Aviancer/amouse/diagrams/amouse-kicad/amouse.sch

## KiCad design diagrams/amouse-kicad/amouse.sch (2021-07-27, an earlier design)

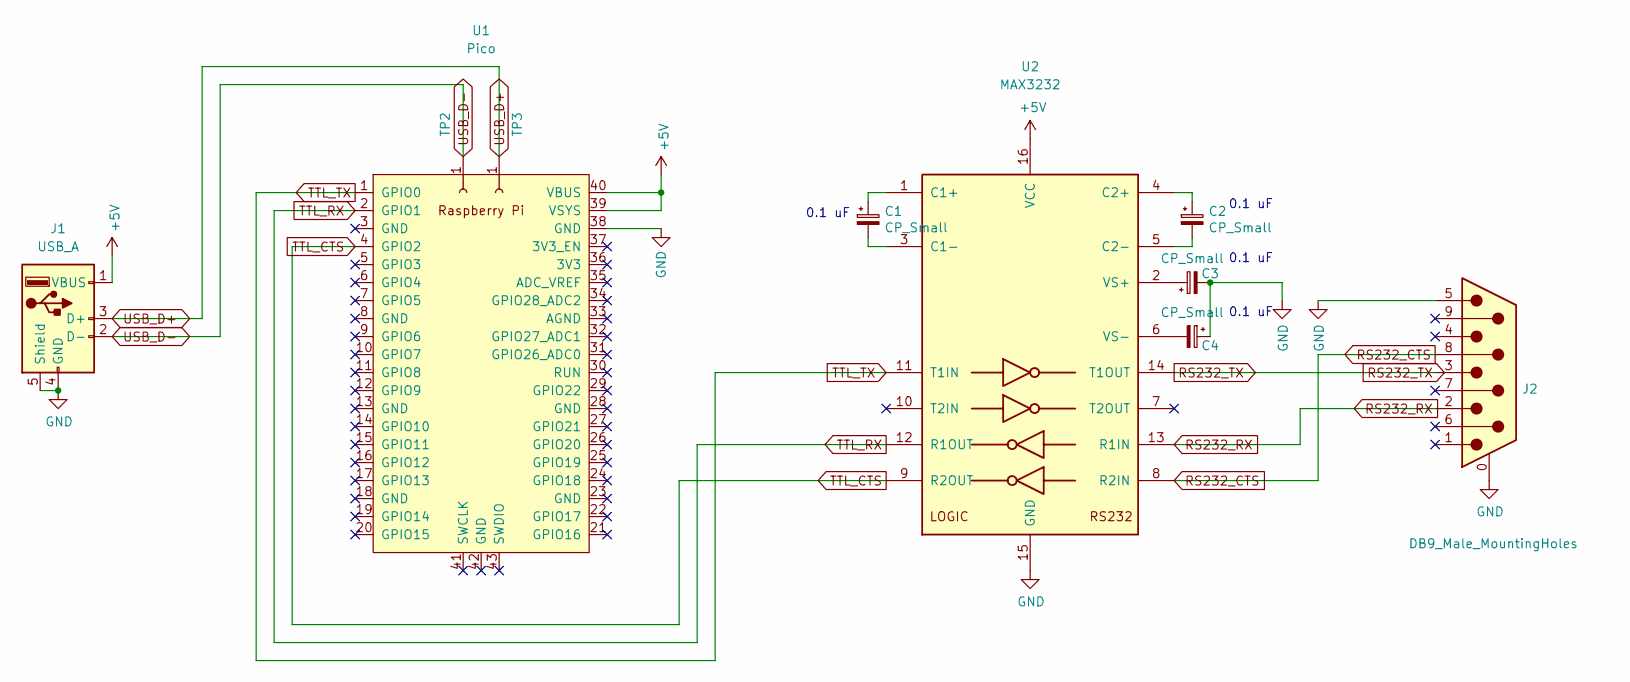
[picture p3: schematic amouse.sch]

Parts:
C1, C2, C3, C4: CP_Small
J1: USB_A
J2: DB9_Male_MountingHoles
TP2: TP2
TP3: TP3
U1: Pico; RPi_Pico_SMD_TH
U2: MAX3232

Connections:
+5V: J1.1 (VBUS), U1.39 (VSYS), U1.40 (VBUS), U2.16 (VCC)
GND: C3.2, C4.1, J1.4 (GND), J1.5 (Shield), J2.0 (PAD), J2.5, U1.38 (GND), U2.15 (GND)
unnamed: C1.1, U2.1 (C1+)
unnamed: C1.2, U2.3 (C1-)
unnamed: C2.1, U2.4 (C2+)
unnamed: C2.2, U2.5 (C2-)
unnamed: C3.1, U2.2 (VS+)
unnamed: C4.2, U2.6 (VS-)
RS232_CTS: J2.8, U2.8 (R2IN)
RS232_RX: J2.2, U2.13 (R1IN)
RS232_TX: J2.3, U2.14 (T1OUT)
TTL_CTS: U1.4 (GPIO2), U2.9 (R2OUT)
TTL_RX: U1.2 (GPIO1), U2.12 (R1OUT)
TTL_TX: U1.1 (GPIO0), U2.11 (T1IN)
USB_D+: J1.3 (D+), TP3.1
USB_D-: J1.2 (D-), TP2.1

Notes on the sheet:
0.1 uF
