Aviancer/amouse/pico/include/usb.c

/*
 * Anachro Mouse, a usb to serial mouse adaptor. Copyright (C) 2021-2025 Aviancer <oss+amouse@skyvian.me>
 *
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
 * You should have received a copy of the GNU Lesser General Public License along with this library; 
 * if not, write to the Free Software Foundation, Inc., 59 Temple Place, Suite 330, Boston, MA 02111-1307 USA
 *
*/

/* Interface adapted from tinyusb examples */

#include "usb.h"

#include "../../shared/mouse.h"


/*** Memory allocations ***/

CFG_TUSB_MEM_SECTION static char serial_in_buffer[64] = { 0 };


/*** USB comms ***/

//static inline void process_mouse_report(mouse_state_t *mouse, hid_mouse_report_t const *p_report);
static void process_generic_report(uint8_t dev_addr, uint8_t instance, uint8_t const* report, uint16_t len);

// Invoked when device with hid interface is mounted
// Report descriptor is also available for use. tuh_hid_parse_report_descriptor()
// can be used to parse common/simple enough descriptor.
// Note: if report descriptor length > CFG_TUH_ENUMERATION_BUFSIZE, it will be skipped
// therefore report_desc = NULL, desc_len = 0
void tuh_hid_mount_cb(uint8_t dev_addr, uint8_t instance, uint8_t const* desc_report, uint16_t desc_len)
{
  // Interface protocol (hid_interface_protocol_enum_t)
  const char* protocol_str[] = { "None", "Keyboard", "Mouse" };
  uint8_t const itf_protocol = tuh_hid_interface_protocol(dev_addr, instance);

  // By default host stack will use activate boot protocol on supported interface.
  // Therefore for this simple example, we only need to parse generic report descriptor (with built-in parser)
  if ( itf_protocol == HID_ITF_PROTOCOL_NONE )
  {
    hid_info[instance].report_count = tuh_hid_parse_report_descriptor(hid_info[instance].report_info, MAX_HID_REPORT, desc_report, desc_len);
  }

  // request to receive report
  // tuh_hid_report_received_cb() will be invoked when report is available
  if ( !tuh_hid_receive_report(dev_addr, instance) )
  {
    // No report available
  }
}

// Invoked when device with hid interface is un-mounted
void tuh_hid_umount_cb(uint8_t dev_addr, uint8_t instance)
{
  // TODO: Clean up after HID device.
  //printf("HID device address = %d, instance = %d is unmounted\r\n", dev_addr, instance);
}

// Invoked when received report from device via interrupt endpoint
void tuh_hid_report_received_cb(uint8_t dev_addr, uint8_t instance, uint8_t const* report, uint16_t len)
{
  uint8_t const itf_protocol = tuh_hid_interface_protocol(dev_addr, instance);

  switch (itf_protocol)
  {
    case HID_ITF_PROTOCOL_KEYBOARD:
      // Ignore keyboard.
      //process_kbd_report( (hid_keyboard_report_t const*) report );
    break;

    case HID_ITF_PROTOCOL_MOUSE:
      collect_mouse_report((hid_mouse_report_t const*) report ); // Shift to report processor context (amouse.c)
    break;

    default:
      // Generic report requires matching ReportID and contents with previous parsed report info
      process_generic_report(dev_addr, instance, report, len);
    break;
  }

  // continue to request to receive report
  if ( !tuh_hid_receive_report(dev_addr, instance) )
  {
    // Error: cannot request to receive report
  }
}


//*** Handle generic USB Report ***/

static void process_generic_report(uint8_t dev_addr, uint8_t instance, uint8_t const* report, uint16_t len) {
  (void) dev_addr;
  (void) len;

  uint8_t const rpt_count = hid_info[instance].report_count;
  tuh_hid_report_info_t* rpt_info_arr = hid_info[instance].report_info;
  tuh_hid_report_info_t* rpt_info = NULL;

  if ( rpt_count == 1 && rpt_info_arr[0].report_id == 0) {
    // Simple report without report ID as 1st byte
    rpt_info = &rpt_info_arr[0];
  }
  else {
    // Composite report, 1st byte is report ID, data starts from 2nd byte
    uint8_t const rpt_id = report[0];

    // Find report id in the arrray
    for(uint8_t i=0; i<rpt_count; i++)
    {
      if (rpt_id == rpt_info_arr[i].report_id) {
        rpt_info = &rpt_info_arr[i];
        break;
      }
    }

    report++;
    len--;
  }

  if (!rpt_info) {
    // Couldn't find the report info for this report
    return;
  }

  // For complete list of Usage Page & Usage checkout src/class/hid/hid.h.
  if (rpt_info->usage_page == HID_USAGE_PAGE_DESKTOP) {
    switch (rpt_info->usage) {
      case HID_USAGE_DESKTOP_KEYBOARD:
        // Ignore keyboards.
      break;

      case HID_USAGE_DESKTOP_MOUSE:
        // Assume mouse follow boot report layout
        collect_mouse_report((hid_mouse_report_t const*) report); // Shift to report processor context (amouse.c)
      break;

      default: break;
    }
  }
}
